Irdroid/Irdroid-HTPC/Photos/1.jpg

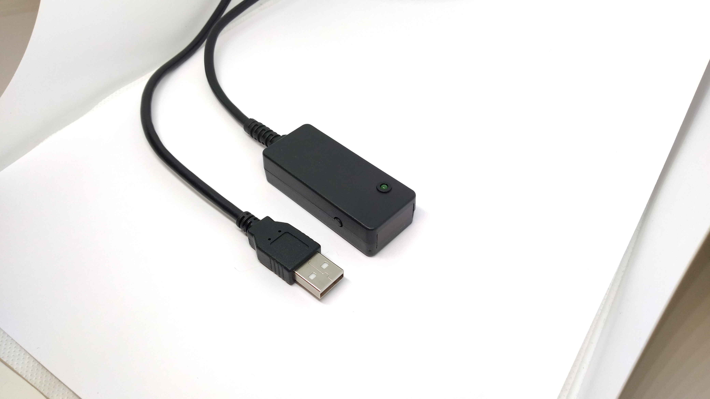
Photos/1.jpg
