Irdroid/Irdroid-HTPC/Photos/2.jpg

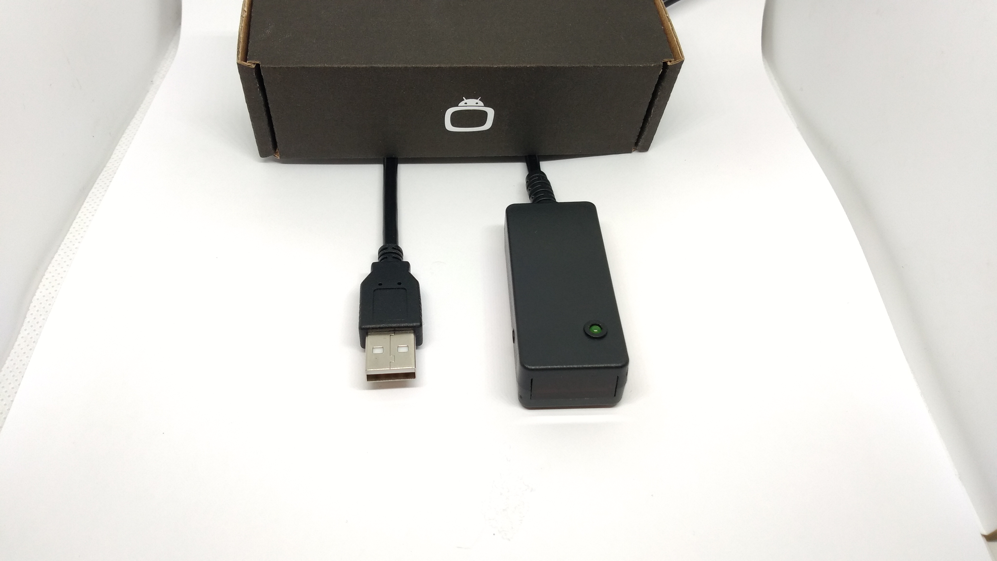
Photos/2.jpg
