Irdroid/Irdroid-HTPC/Photos/3.jpg

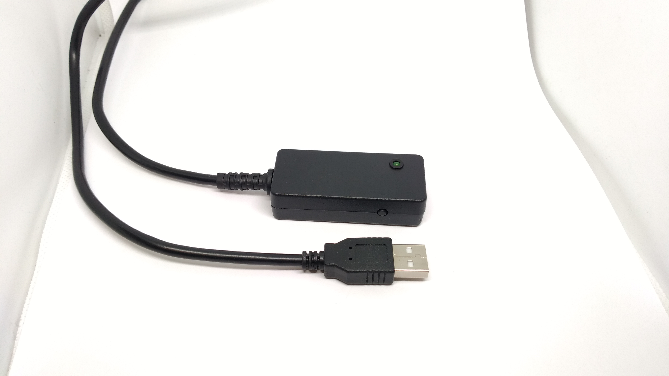
Photos/3.jpg
