Irdroid/Irdroid-HTPC/Photos/irdroid-htpc-universal-infrared-receiver-2 (Custom).png

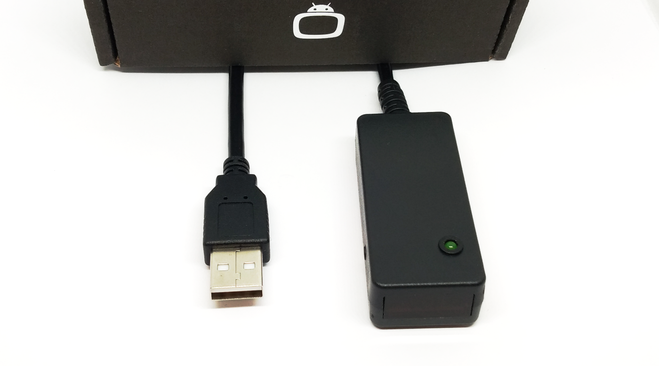
Photos/irdroid-htpc-universal-infrared-receiver-2 (Custom).png
