Irdroid/Irdroid-HTPC/Photos/irdroid-htpc-universal-infrared-receiver-3 (Custom).png

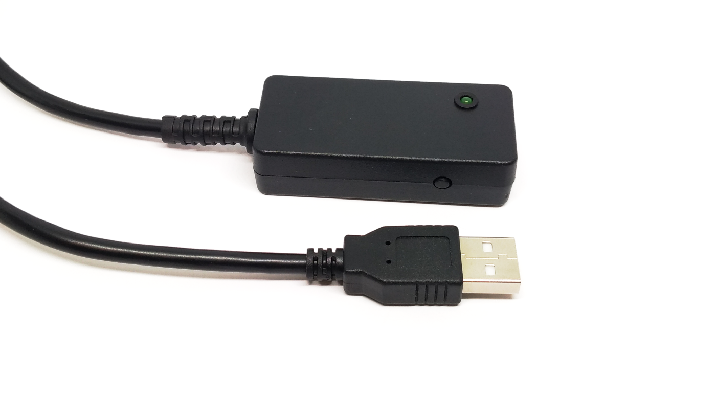
Photos/irdroid-htpc-universal-infrared-receiver-3 (Custom).png
